sparkfun/LiPo_Charger_Booster_5V_1A/Documentation/Hookup Photos/bothon.png

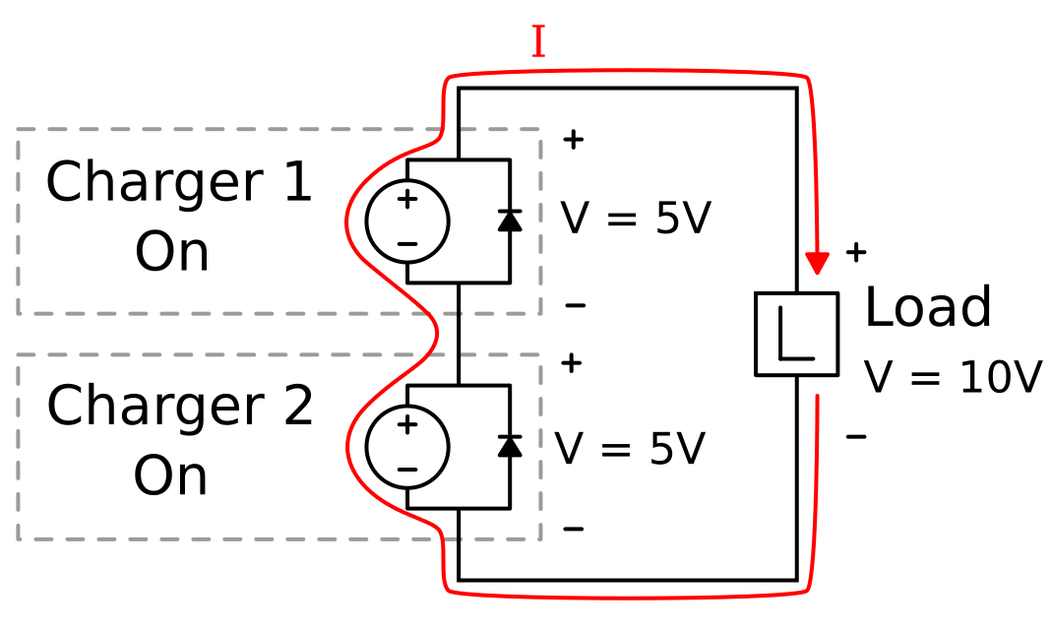
Documentation/Hookup Photos/bothon.png
