sparkfun/LiPo_Charger_Booster_5V_1A/Documentation/Hookup Photos/botside_nonotes.jpg

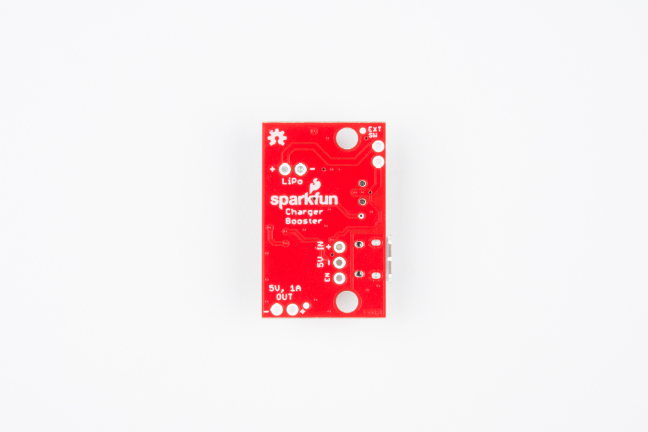
Documentation/Hookup Photos/botside_nonotes.jpg
