sparkfun/LiPo_Charger_Booster_5V_1A/Documentation/Hookup Photos/bypassDrawing.png

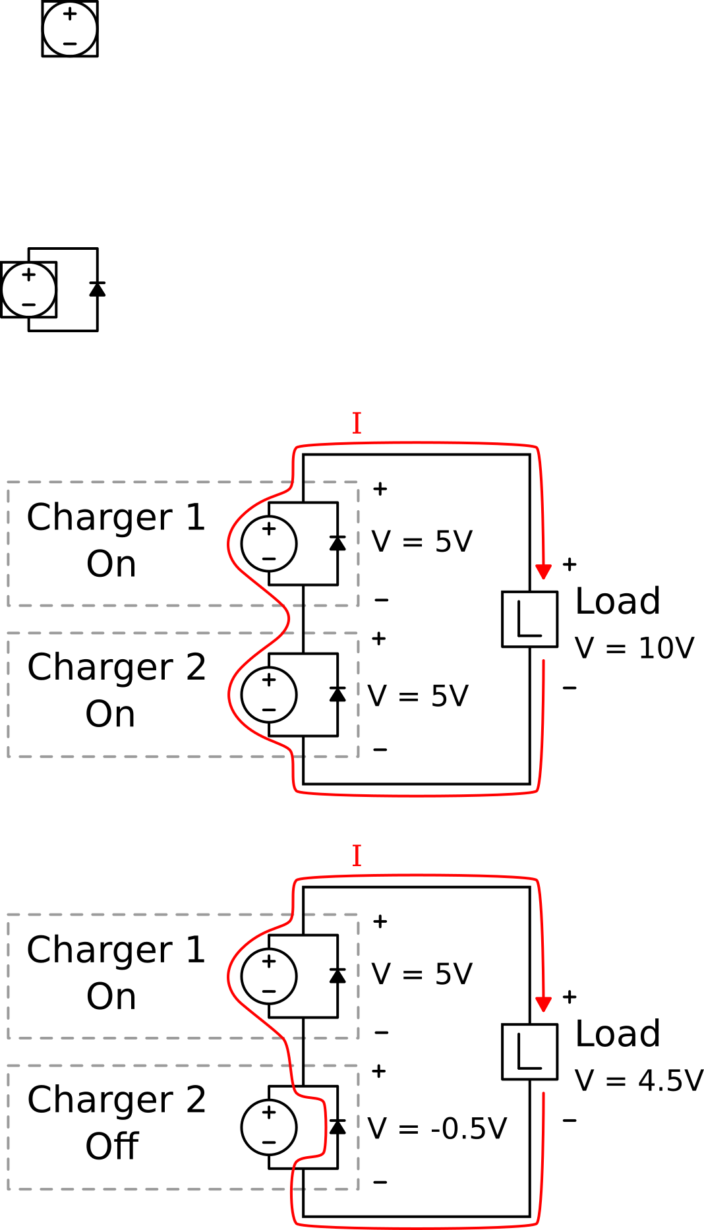
Documentation/Hookup Photos/bypassDrawing.png
