sparkfun/LiPo_Charger_Booster_5V_1A/Documentation/Hookup Photos/currentGraph.png

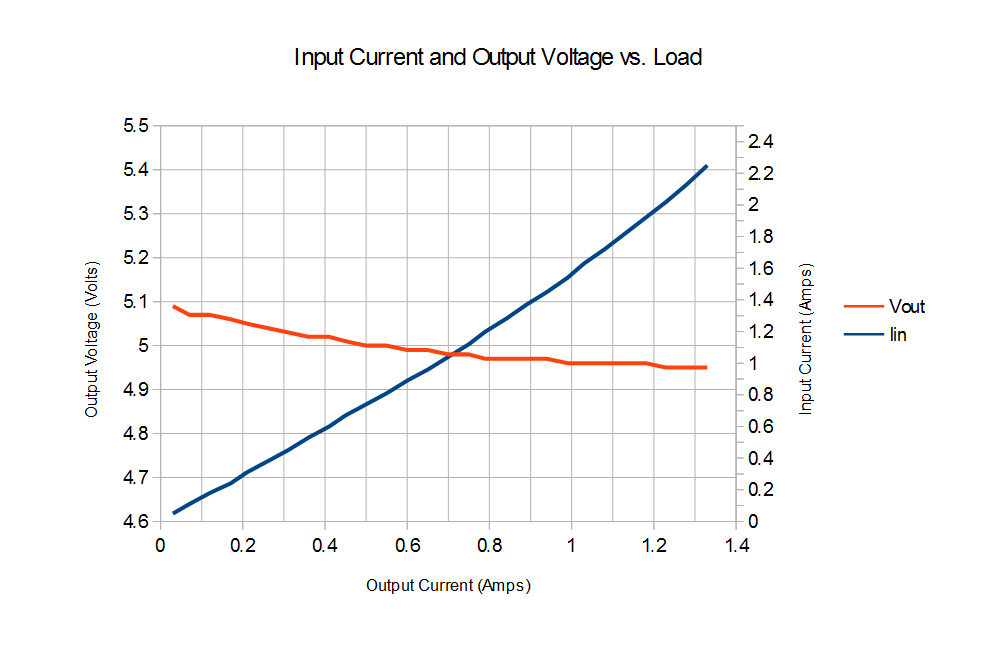
Documentation/Hookup Photos/currentGraph.png
