sparkfun/LiPo_Charger_Booster_5V_1A/Documentation/Hookup Photos/EfficiencyGraph.png

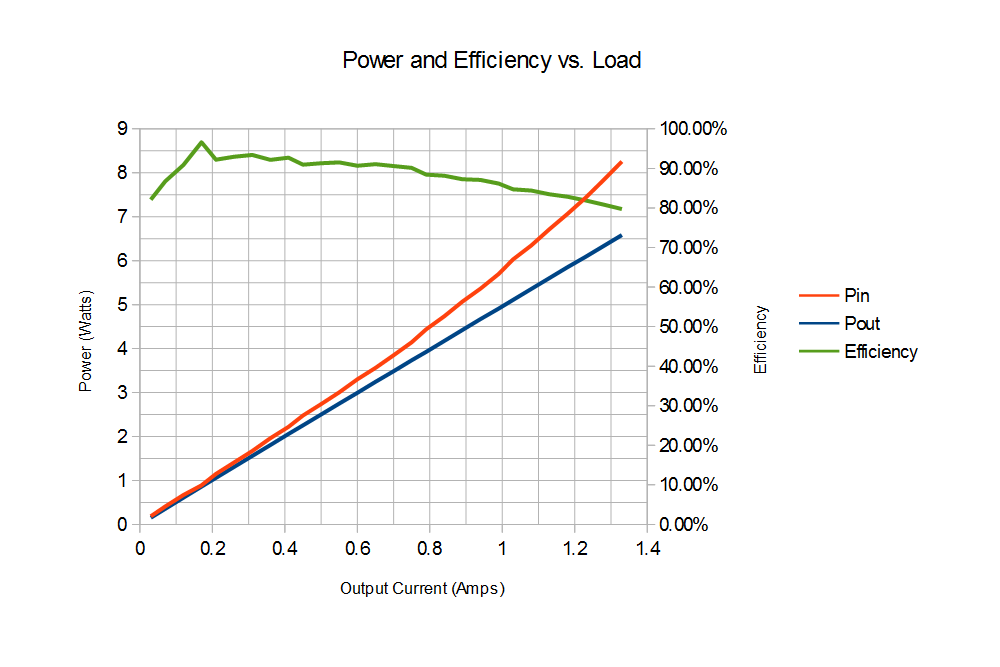
Documentation/Hookup Photos/EfficiencyGraph.png
