sparkfun/LiPo_Charger_Booster_5V_1A/Documentation/Hookup Photos/onedead.png

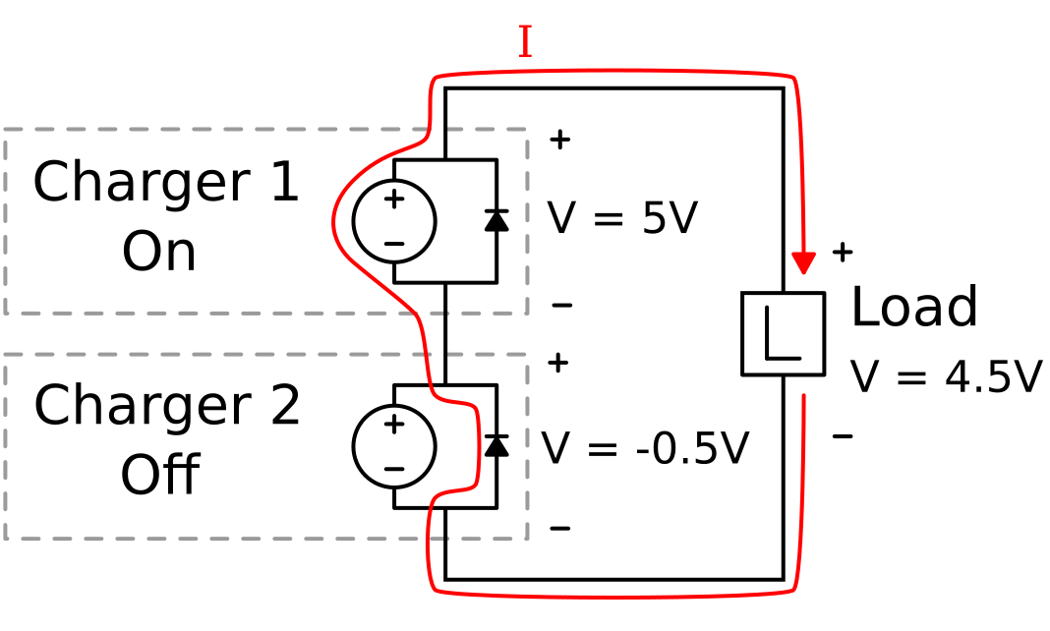
Documentation/Hookup Photos/onedead.png
